TunaHero/TheThresher/Files/STLs/Tertiary Color/Trigger Link.STL

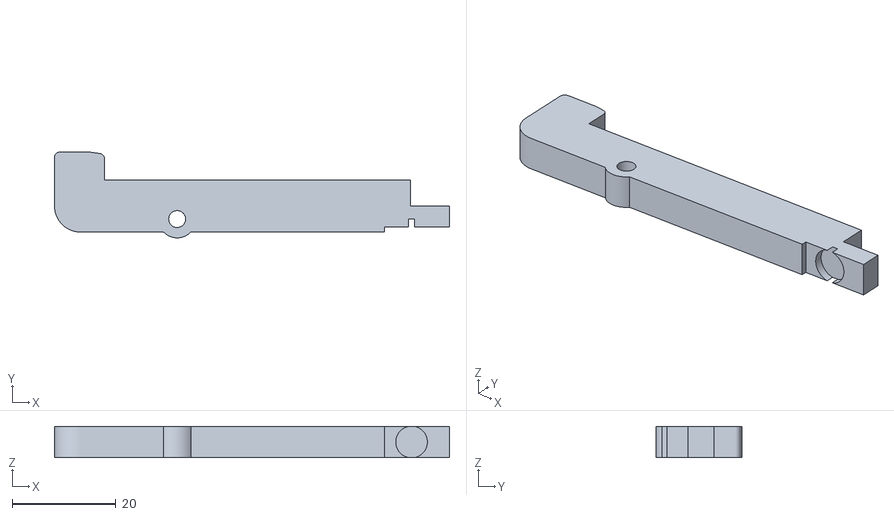
[picture p32: CAD file, 2023-04-25]
Files/STLs/Tertiary Color/Trigger Link.STL
76.1 x 16.5 x 6.00
