TunaHero/TheThresher/Files/STLs/Primary Color/Upper Rail Support.STL

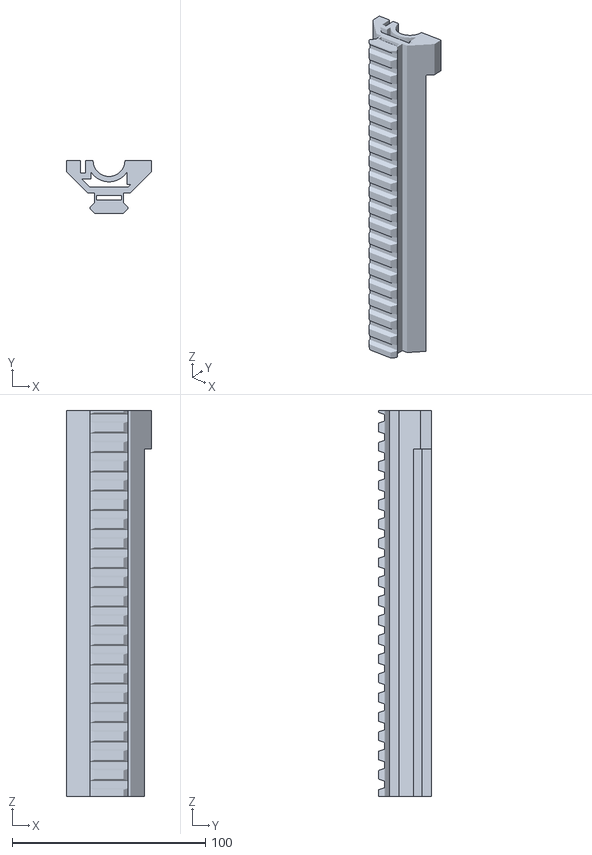
[picture p33: CAD file, 2023-04-13]
Files/STLs/Primary Color/Upper Rail Support.STL
44.1 x 27.3 x 200.0
