TunaHero/TheThresher/Files/STLs/Secondary Color/Lower Rail Support.STL

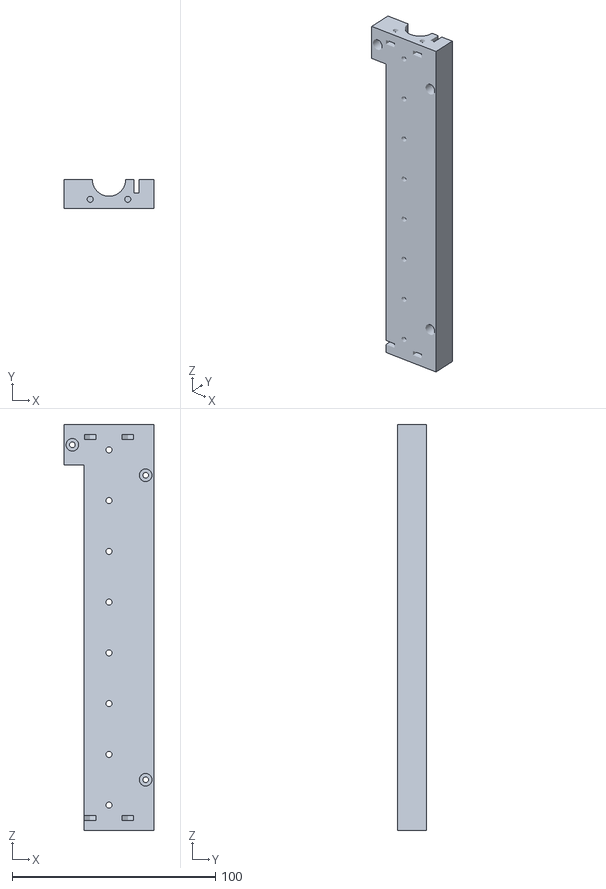
[picture p34: CAD file, 2023-04-13]
Files/STLs/Secondary Color/Lower Rail Support.STL
44.1 x 14.2 x 200.0
