TunaHero/TheThresher/Files/STLs/Tertiary Color/Plunger Cap.STL

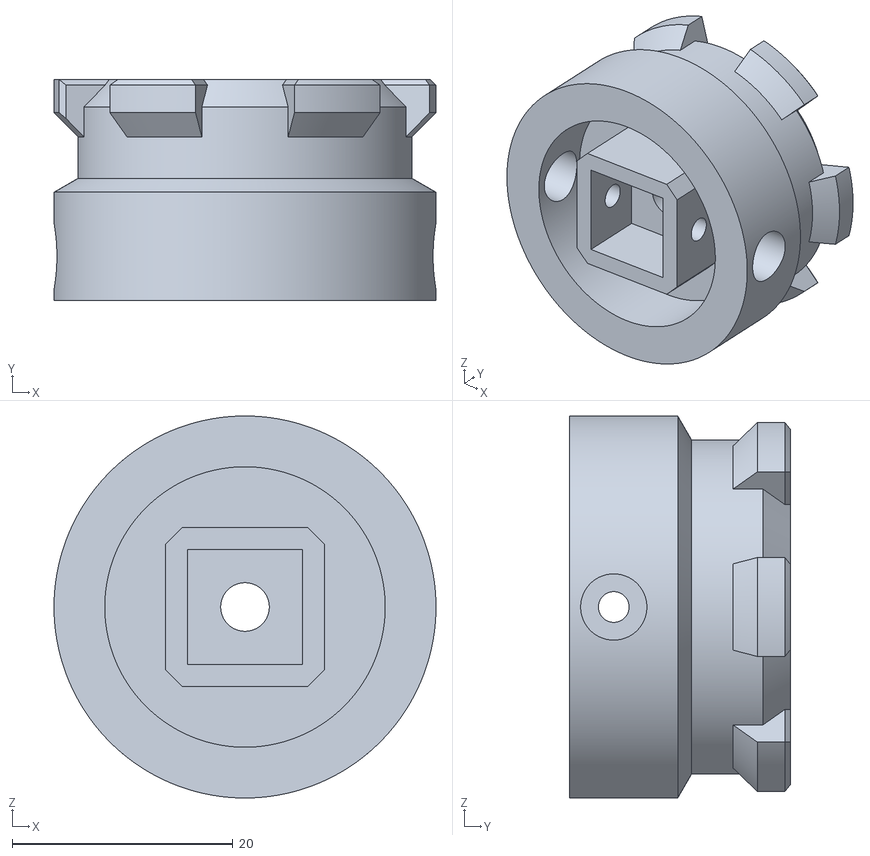
[picture p35: CAD file, 2023-04-13]
Files/STLs/Tertiary Color/Plunger Cap.STL
34.6 x 20.0 x 34.6
