TunaHero/TheThresher/Files/STLs/Tertiary Color/Plunger Cup.STL

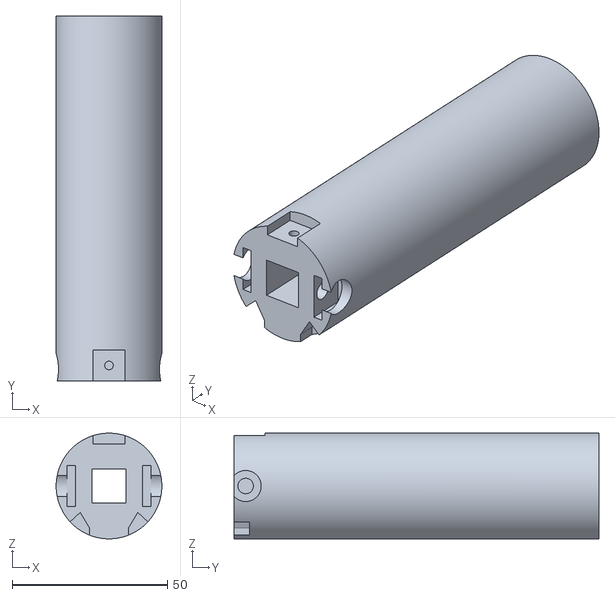
[picture p36: CAD file, 2023-04-13]
Files/STLs/Tertiary Color/Plunger Cup.STL
34.0 x 117.4 x 34.0
