TunaHero/TheThresher/Files/STLs/Tertiary Color/Plunger Cup Cap.STL

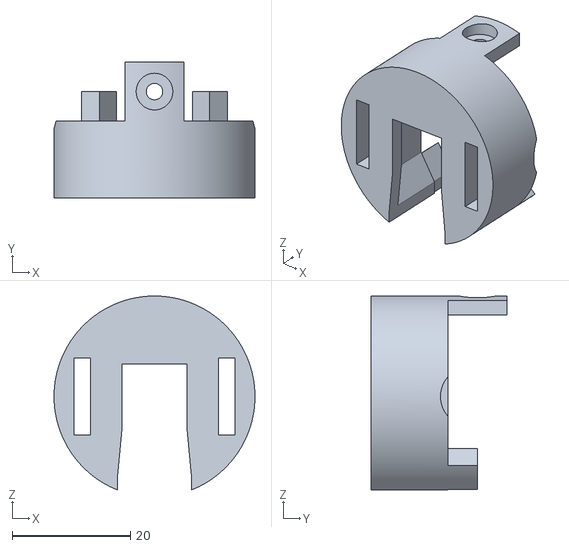
[picture p37: CAD file, 2023-04-13]
Files/STLs/Tertiary Color/Plunger Cup Cap.STL
34.0 x 23.0 x 32.8
